buuczech/Motobuttons/firmware/Moto_Buttons/src/MyBfButton.cpp

/*
 * MyBfButton.cpp
 * Standalone digital button module handle various button events
 * Copyright (c) 2019 Mickey Chan
 *
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
 * Developed for Arduino-ESP32
 * Created by Mickey Chan (developer AT comicparty.com)
 */
#include "bluefruit.h"
#include "Arduino.h"
#include "MyBfButton.h"

MyBfButton::MyBfButton(button_mode_t mode, uint8_t pin, bool pullup, uint8_t buttonLogic, uint8_t keyCodeSingle, uint8_t keyCodeLong, uint8_t keyCodeDouble) {
  this->_id = pin;
  this->_mode = mode;
  if (this->_mode == MyBfButton::STANDALONE_DIGITAL) {
    if (pullup) {
      pinMode(this->_id, INPUT_PULLUP);
    } else {
      pinMode(this->_id, INPUT); // for external pullup or pulldown
    }
    this->_buttonLogic = buttonLogic;
  }
	this->_keyCodeSingle = keyCodeSingle;
	this->_keyCodeLong = keyCodeLong;
	this->_keyCodeDouble = keyCodeDouble;
}

MyBfButton& MyBfButton::onPress(callback_t callback) {
  this->_onPressCallback = callback;
  return *this;
}

MyBfButton& MyBfButton::onDoublePress(callback_t callback, unsigned long timeout) {
  this->_onDoublePressCallback = callback;
  this->_doublePressTimeout = timeout;
  return *this;
}

MyBfButton& MyBfButton::onPressFor(callback_t callback, unsigned long timeout) {
  this->_onPressForCallback = callback;
  this->_pressForTimeout = timeout;
  return *this;
}

MyBfButton& MyBfButton::updateState(button_state_t state) {
  this->_prevState = this->_state;
  this->_state = state;
  return *this;
}

// only for standalone digital button
void MyBfButton::read() {
  if (this->_mode != MyBfButton::STANDALONE_DIGITAL) return;
  unsigned long curTime = millis();
  if (curTime - this->_lastLoop >= this->_loopInterval) {
    this->_lastLoop = curTime;
    int x = digitalRead(this->_id);
    if (x == this->_buttonLogic) {
      this->updateState(MyBfButton::PRESSING);
    } else {
      this->updateState(MyBfButton::IDLE);
    }
    this->loop();
  }
}

void MyBfButton::loop() {
  unsigned long curTime = millis();
  // debouncing
  if (this->_prevState == MyBfButton::IDLE && this->_state == MyBfButton::PRESSING) {
    this->_isDebouncing = true;
    return;
  }
  
  // double press timeout, may trigger last single press event (if no pressFor callback)
  if (this->_pressCount > 0 &&
    !(this->_onDoublePressCallback && curTime - this->_firstPressedAt <= this->_doublePressTimeout) &&
    !(this->_onPressForCallback && this->_pressedSince != 0 && this->_state == MyBfButton::PRESSING)) {
      if (this->_onPressCallback) this->_onPressCallback(this, MyBfButton::SINGLE_PRESS);
      this->_pressCount = 0;
      this->_firstPressedAt = 0;
  }
  
  if (this->_prevState == MyBfButton::PRESSING && this->_state == MyBfButton::PRESSING) {
    // confirm pressed
    if (this->_isDebouncing) {
      this->_pressCount++;
      if (this->_firstPressedAt == 0) this->_firstPressedAt = curTime;
      if (this->_pressedSince == 0) this->_pressedSince = curTime;
      this->_isDebouncing = false;
    }
    
    // Press For
    if (this->_onPressForCallback && this->_pressCount > 0 &&
      (curTime - this->_pressedSince >= this->_pressForTimeout)) {
        this->_onPressForCallback(this, MyBfButton::LONG_PRESS);
        this->_pressCount = 0;
        this->_firstPressedAt = 0;
        this->_pressedSince = 0;
        return;
    }
    
    // Double Press
    if (this->_onDoublePressCallback && this->_pressCount > 1 &&
      (curTime - this->_firstPressedAt <= this->_doublePressTimeout)) {
        this->_onDoublePressCallback(this, MyBfButton::DOUBLE_PRESS);
        this->_pressCount = 0;
        this->_firstPressedAt = 0;
        return;
    }
  }
  
  // release the button
  if (this->_prevState == MyBfButton::PRESSING && this->_state == MyBfButton::IDLE) {
    this->_pressedSince = 0; // reset pressFor timer
  }
}

uint8_t MyBfButton::getID() {
  return this->_id;
}

uint8_t MyBfButton::getKeyCodeSingle() {
	return this->_keyCodeSingle;
}

uint8_t MyBfButton::getKeyCodeLong() {
	return this->_keyCodeLong;
}

uint8_t MyBfButton::getKeyCodeDouble() {
	return this->_keyCodeDouble;
}

uint8_t MyBfButton::getPin() {
  return this->getID();
}
